hackwinkel/programmer/KiCAD_PCB/programmer.sch

## KiCad design KiCAD_PCB/programmer.sch (2020-08-23)

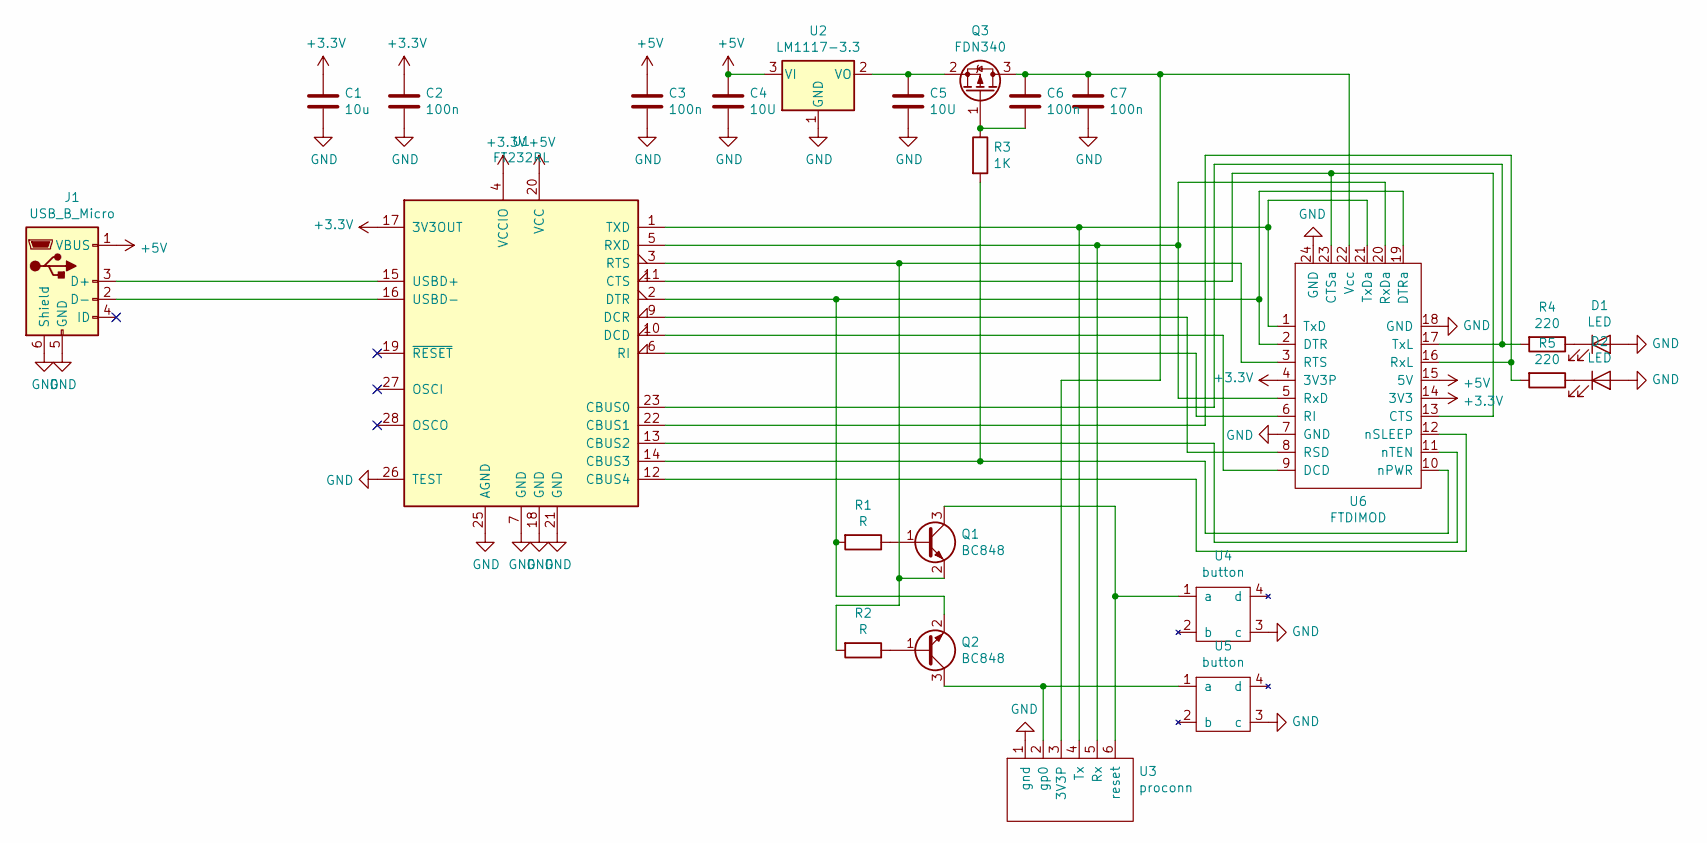
[picture p2: schematic programmer.sch]

Parts:
C1: 10u; C_0805_2012Metric_Pad1.15x1.40mm_HandSolder
C2, C3, C6, C7: 100n; C_0805_2012Metric_Pad1.15x1.40mm_HandSolder
C4, C5: 10U; C_0805_2012Metric_Pad1.15x1.40mm_HandSolder
D1, D2: LED; C_1206_3216Metric_Pad1.42x1.75mm_HandSolder
J1: USB_B_Micro; USB_Mini-B
Q1, Q2: BC848; SOT-23
Q3: FDN340; SOT-23_Handsoldering
R1, R2: R; C_0805_2012Metric_Pad1.15x1.40mm_HandSolder
R3: 1K; C_0805_2012Metric_Pad1.15x1.40mm_HandSolder
R4, R5: 220; C_0805_2012Metric_Pad1.15x1.40mm_HandSolder
U1: FT232RL; SSOP-28_5.3x10.2mm_P0.65mm
U2: LM1117-3.3; SOT-223-3_TabPin2
U3: proconn
U4, U5: button; sw12
U6: FTDIMOD; ftdimod

Connections:
+3.3V: C1.1, C2.1, U1.4 (VCCIO), U1.17 (3V3OUT), U6.4 (3V3P), U6.14 (3V3)
+5V: C3.1, C4.1, J1.1 (VBUS), U1.20 (VCC), U2.3 (VI), U6.15 (5V)
GND: C1.2, C2.2, C3.2, C4.2, C5.2, C7.2, D1.2 (A), D2.2 (A), J1.5 (GND), J1.6 (Shield), U1.7 (GND), U1.18 (GND), U1.21 (GND), U1.25 (AGND), U1.26 (TEST), U2.1 (GND), U3.1 (gnd), U4.3 (c), U5.3 (c), U6.7 (GND), U6.18 (GND), U6.24 (GND)
unnamed: C5.1, Q3.2 (S), U2.2 (VO)
unnamed: C6.1, C7.1, Q3.3 (D), U3.3 (3V3P), U6.22 (Vcc)
unnamed: C6.2, Q3.1 (G), R3.1
unnamed: D1.1 (K), R4.1
unnamed: D2.1 (K), R5.1
unnamed: J1.2 (D-), U1.16 (USBD-)
unnamed: J1.3 (D+), U1.15 (USBD+)
unnamed: Q1.1 (B), R1.1
unnamed: Q1.2 (E), R2.2, U1.3 (RTS), U6.3 (RTS)
unnamed: Q1.3 (C), U3.6 (reset), U4.1 (a)
unnamed: Q2.1 (B), R2.1
unnamed: Q2.2 (E), R1.2, U1.2 (DTR), U6.2 (DTR), U6.19 (DTRa)
unnamed: Q2.3 (C), U3.2 (gp0), U5.1 (a)
unnamed: R3.2, U1.14 (CBUS3), U6.10 (nPWR)
unnamed: R4.2, U1.23 (CBUS0), U6.17 (TxL)
unnamed: R5.2, U1.22 (CBUS1), U6.16 (RxL)
unnamed: U1.1 (TXD), U3.4 (Tx), U6.1 (TxD), U6.21 (TxDa)
unnamed: U1.5 (RXD), U3.5 (Rx), U6.5 (RxD), U6.20 (RxDa)
unnamed: U1.6 (RI), U6.6 (RI)
unnamed: U1.9 (DCR), U6.8 (RSD)
unnamed: U1.10 (DCD), U6.9 (DCD)
unnamed: U1.11 (CTS), U6.13 (CTS), U6.23 (CTSa)
unnamed: U1.12 (CBUS4), U6.12 (nSLEEP)
unnamed: U1.13 (CBUS2), U6.11 (nTEN)
